KarlZeilhofer/rs232-sniffer/kicad/render/2020-11-13_001.png

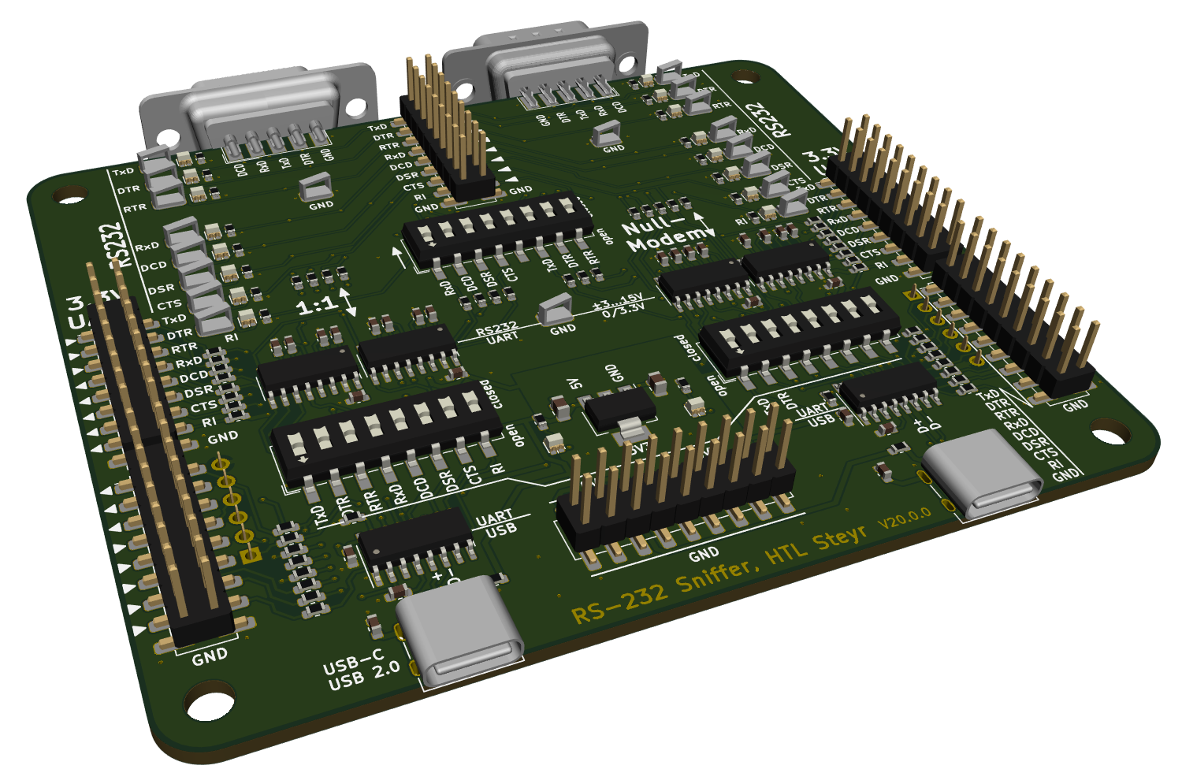
kicad/render/2020-11-13_001.png
