KarlZeilhofer/rs232-sniffer/kicad/render/2020-11-13_004.png

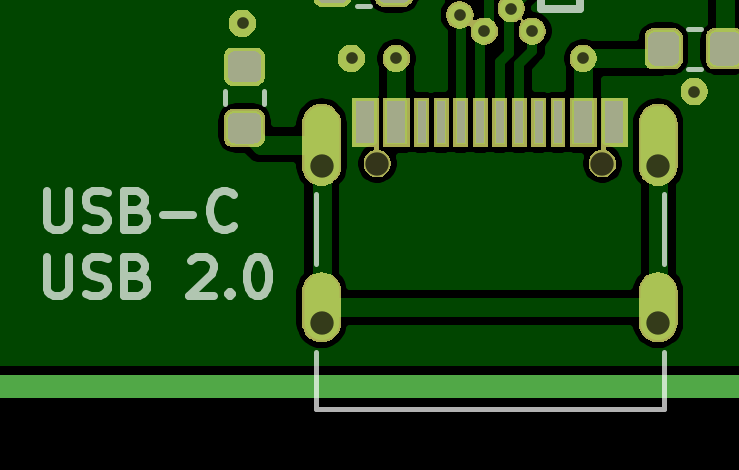
kicad/render/2020-11-13_004.png
